OpenMANET/enclosures/OpenChubNET/stl/openMANET_top_usbc_rj45_ntype_sma.stl

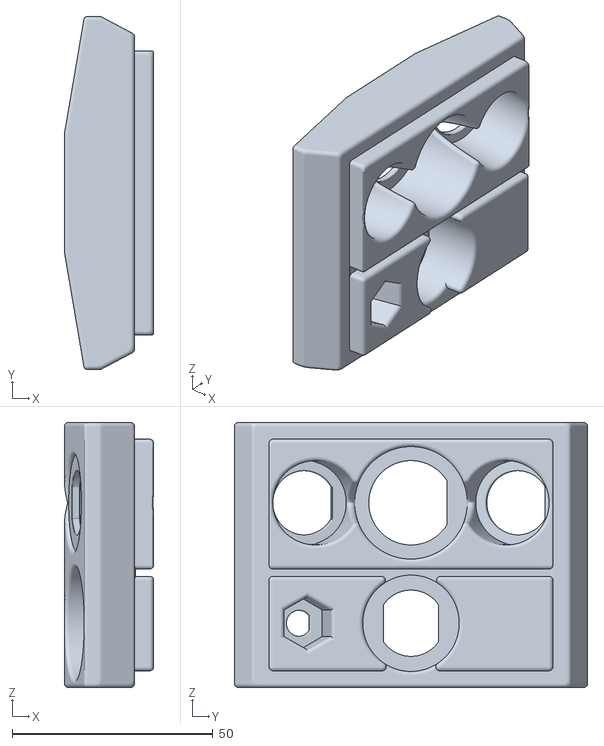
[picture p15: CAD file, 2025-11-21]
OpenChubNET/stl/openMANET_top_usbc_rj45_ntype_sma.stl
22.2 x 88.0 x 66.0
