OpenMANET/enclosures/OpenChubNET/stl/openMANET_stencil_sma.stl

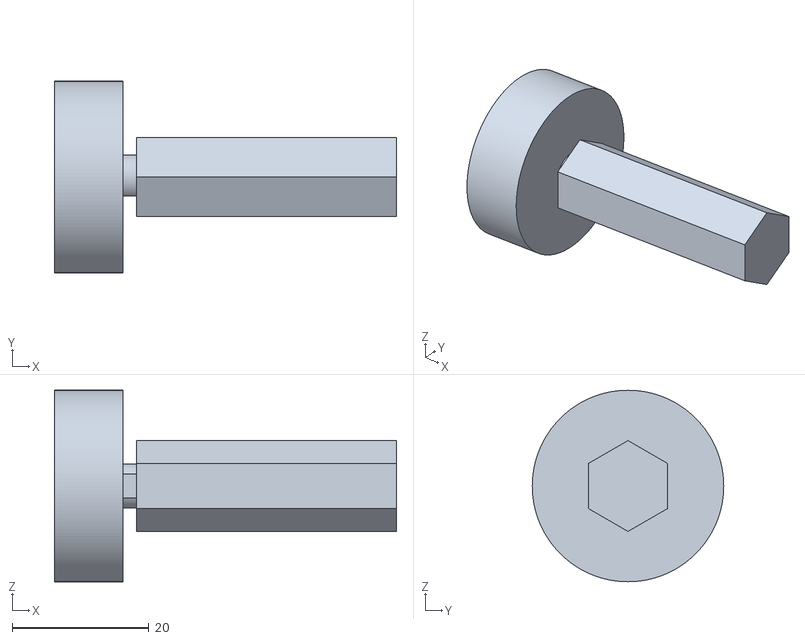
[picture p16: CAD file, 2025-11-20]
OpenChubNET/stl/openMANET_stencil_sma.stl
50.0 x 28.0 x 28.0
